coxifred/PimpMyEpson/sources/MemoryWebResources.h

// Les images avec HxD
const char MIME_png[] PROGMEM = "image/png";
const char DATA_logo[33435] PROGMEM = {
	0x89, 0x50, 0x4E, 0x47, 0x0D, 0x0A, 0x1A, 0x0A, 0x00, 0x00, 0x00, 0x0D,
	0x49, 0x48, 0x44, 0x52, 0x00, 0x00, 0x00, 0xC3, 0x00, 0x00, 0x00, 0xC3,
	0x08, 0x06, 0x00, 0x00, 0x00, 0x3F, 0x7F, 0xA5, 0xAA, 0x00, 0x00, 0x20,
	0x00, 0x49, 0x44, 0x41, 0x54, 0x78, 0x9C, 0xED, 0x7D, 0x77, 0x7C, 0x5C,
	0xC5, 0xB9, 0xF6, 0x33, 0xBB, 0x2B, 0xAD, 0x7A, 0x97, 0xAC, 0x66, 0x5B,
	0xB2, 0x6C, 0xCB, 0xDD, 0x72, 0x95, 0x71, 0xC1, 0x05, 0x03, 0xC1, 0xF4,
	0x66, 0x7A, 0x09, 0xA1, 0x86, 0x84, 0x84, 0x0B, 0x21, 0x81, 0x10, 0xE0,
	0x26, 0x21, 0x24, 0xA1, 0x93, 0x70, 0x29, 0x09, 0x01, 0x42, 0xC0, 0x84,
	0x5E, 0x0C, 0xA6, 0x3B, 0xB8, 0xDB, 0xD8, 0xB8, 0x4A, 0x2E, 0xB2, 0x65,
	0xC9, 0xB2, 0xAC, 0xDE, 0xA5, 0x95, 0xB6, 0xCE, 0xF7, 0xC7, 0x99, 0x99,
	0x33, 0xE7, 0xEC, 0x59, 0x59, 0x5A, 0xFB, 0xBB, 0x96, 0xAE, 0xE7, 0xF1,
	0x4F, 0xDE, 0xDD, 0xE7, 0x4C, 0x9F, 0x79, 0xE7, 0x7D, 0xA7, 0x1E, 0x42,
	0x29, 0xA5, 0x50, 0x50, 0x50, 0x80, 0xED, 0x44, 0x27, 0x40, 0x41, 0x61,
	0xA0, 0x40, 0x09, 0x83, 0x82, 0x02, 0x83, 0x12, 0x06, 0x05, 0x05, 0x06,
	0x25, 0x0C, 0x0A, 0x0A, 0x0C, 0x4A, 0x18, 0x14, 0x14, 0x18, 0x94, 0x30,
	0x28, 0x28, 0x30, 0x28, 0x61, 0x50, 0x50, 0x60, 0x50, 0xC2, 0xA0, 0xA0,
	0xC0, 0xA0, 0x84, 0x41, 0x41, 0x81, 0x41, 0x09, 0x83, 0x82, 0x02, 0x83,
	0x12, 0x06, 0x05, 0x05, 0x06, 0x25, 0x0C, 0x0A, 0x0A, 0x0C, 0x4A, 0x18,
	0x14, 0x14, 0x18, 0x94, 0x30, 0x28, 0x28, 0x30, 0x28, 0x61, 0x50, 0x50,
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
  0x69, 0x45, 0xFE, 0x64, 0x98, 0x8D, 0x7A, 0x6E, 0xA3, 0x61, 0xE6, 0xCB,
  0x63, 0xFE, 0x60, 0x01, 0x3D, 0x3F, 0x4A, 0x7D, 0x96, 0xF3, 0xE6, 0xE6,
  0x00, 0xCD, 0x1D, 0xB3, 0x57, 0x17, 0xC6, 0x85, 0x92, 0x91, 0x9E, 0x37,
  0xEA, 0xB6, 0x9D, 0x0B, 0x7C, 0x73, 0x73, 0xC3, 0x69, 0x85, 0x99, 0x3F,
  0x56, 0x23, 0xA2, 0xAA, 0xE0, 0x73, 0x12, 0x78, 0x9A, 0x0D, 0xD2, 0x1F,
  0x7C, 0xB9, 0xE2, 0xEB, 0x82, 0xBF, 0x40, 0x81, 0xBD, 0xAF, 0xC6, 0x8F,
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
};
